akshaykalia-chd/Px-Rack/STL/PLA_PETG/25x265 Banding.stl

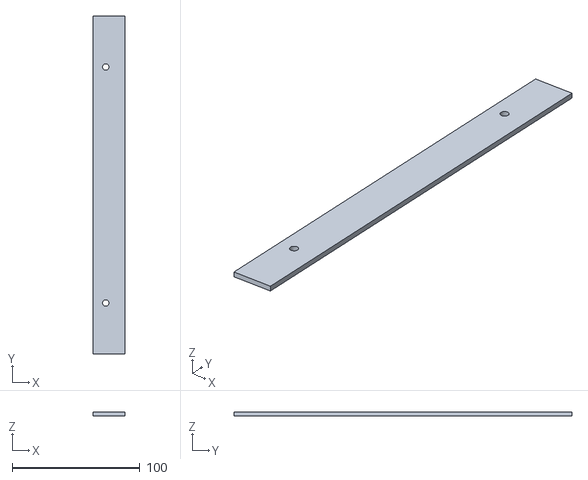
[picture p21: CAD file, 2026-06-15]
STL/PLA_PETG/25x265 Banding.stl
25.0 x 265.0 x 3.00
