akshaykalia-chd/Px-Rack/STL/ABS/Power-Mount-Back-Plate.stl

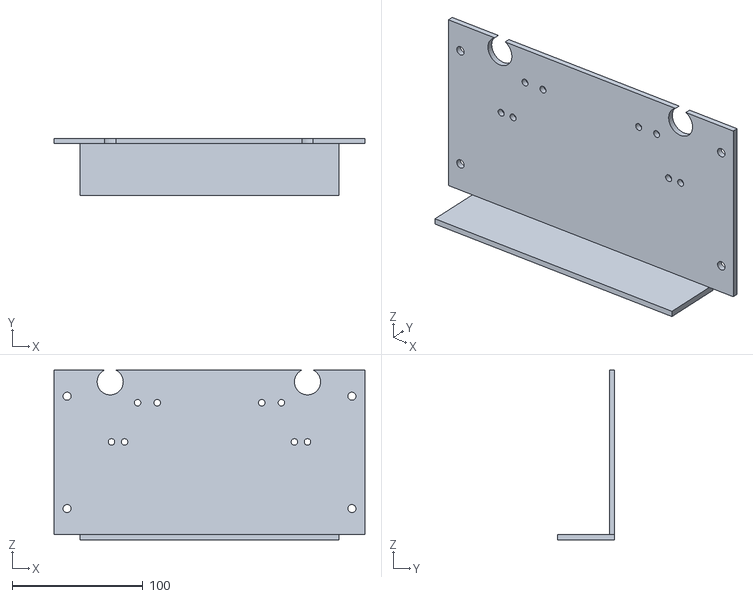
[picture p22: CAD file, 2026-06-15]
STL/ABS/Power-Mount-Back-Plate.stl
238.0 x 44.0 x 130.0
