akshaykalia-chd/Px-Rack/STL/PLA_PETG/5mm-Swith-bush.stl

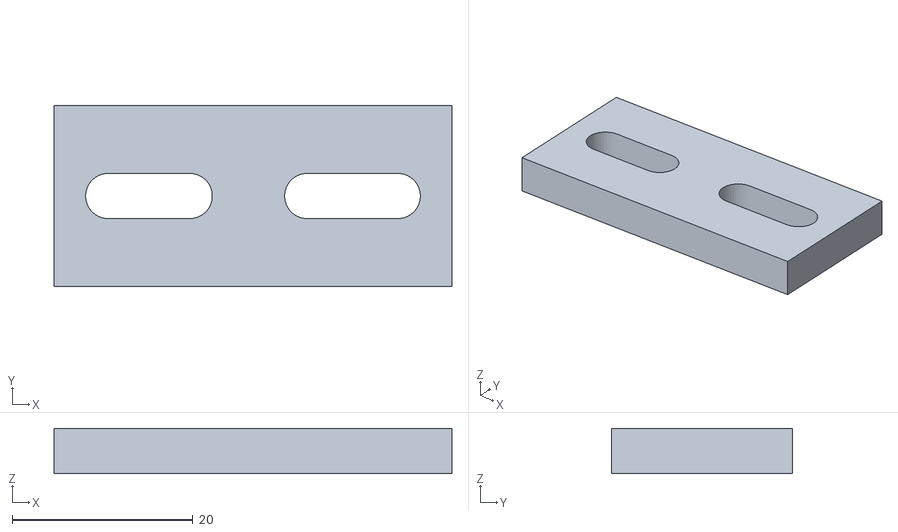
[picture p23: CAD file, 2026-06-15]
STL/PLA_PETG/5mm-Swith-bush.stl
44.0 x 20.0 x 5.00
