akshaykalia-chd/Px-Rack/STL/ABS/Foot.stl

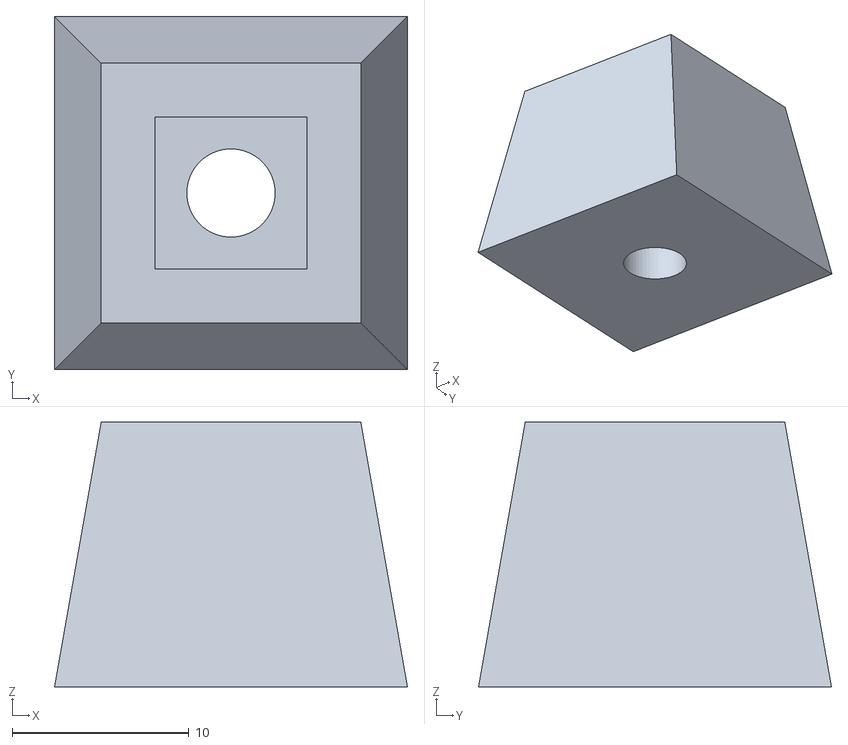
[picture p24: CAD file, 2026-05-14]
STL/ABS/Foot.stl
20.0 x 20.0 x 15.0
