akshaykalia-chd/Px-Rack/STL/PLA_PETG/Back-Cover.stl

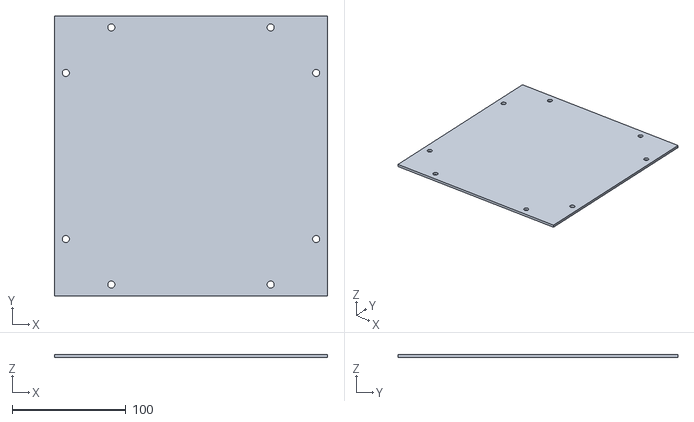
[picture p25: CAD file, 2026-06-15]
STL/PLA_PETG/Back-Cover.stl
240.0 x 246.0 x 3.00
