akshaykalia-chd/Px-Rack/STL/ABS/Power-Mount-PCB-Holder-Plate.stl

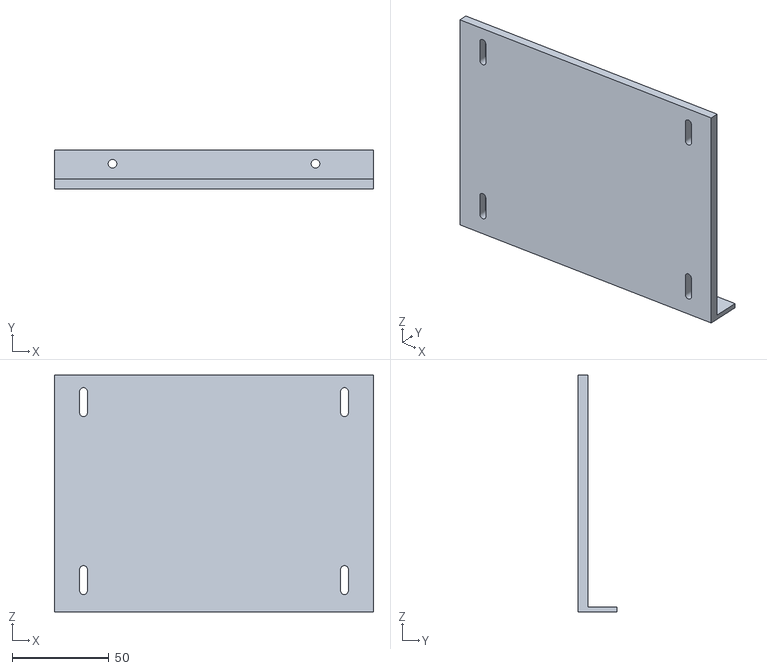
[picture p26: CAD file, 2026-04-22]
STL/ABS/Power-Mount-PCB-Holder-Plate.stl
165.0 x 20.0 x 122.5
