akshaykalia-chd/Px-Rack/STL/PLA_PETG/Bottom-cover.stl

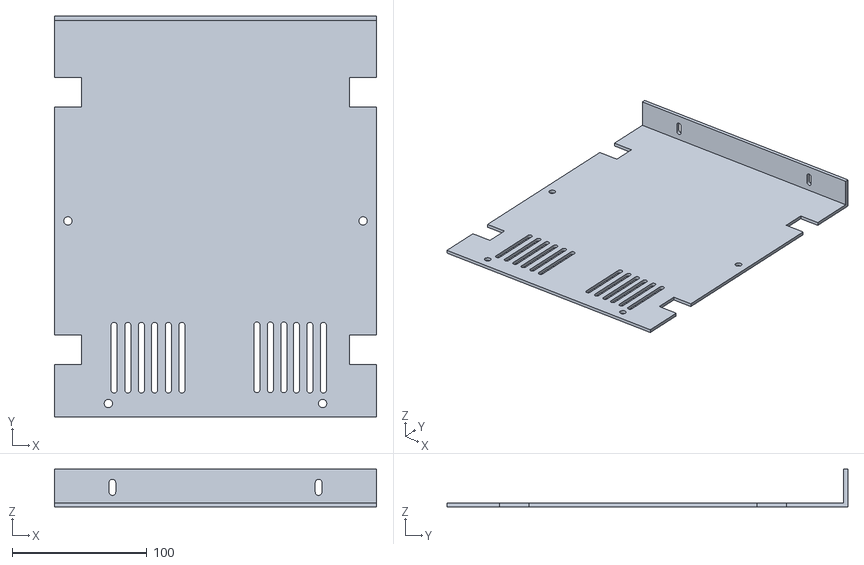
[picture p27: CAD file, 2026-06-15]
STL/PLA_PETG/Bottom-cover.stl
239.0 x 297.5 x 28.0
