akshaykalia-chd/Px-Rack/STL/ABS/Power-Mount-Base.stl

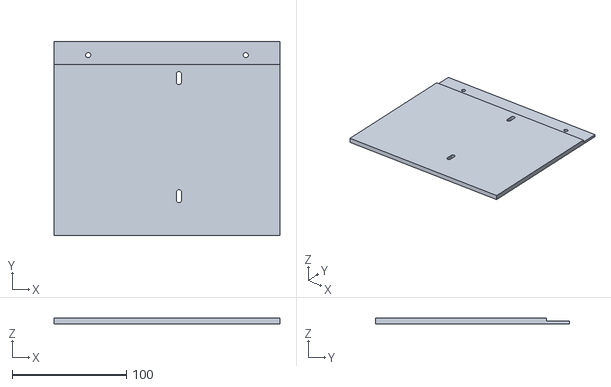
[picture p28: CAD file, 2026-04-22]
STL/ABS/Power-Mount-Base.stl
198.0 x 170.0 x 5.00
