akshaykalia-chd/Px-Rack/STL/PLA_PETG/Left-Side-Panel-120mm-Fan-Power-Cut.stl

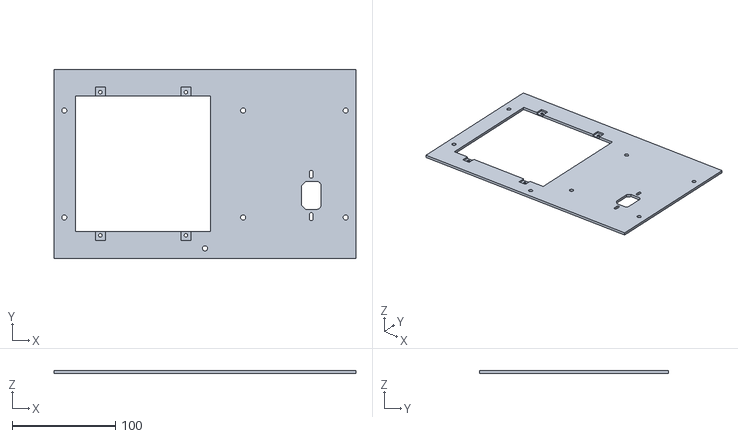
[picture p29: CAD file, 2026-06-15]
STL/PLA_PETG/Left-Side-Panel-120mm-Fan-Power-Cut.stl
293.0 x 183.8 x 3.00
