akshaykalia-chd/Px-Rack/STL/PLA_PETG/Top-Cover.stl

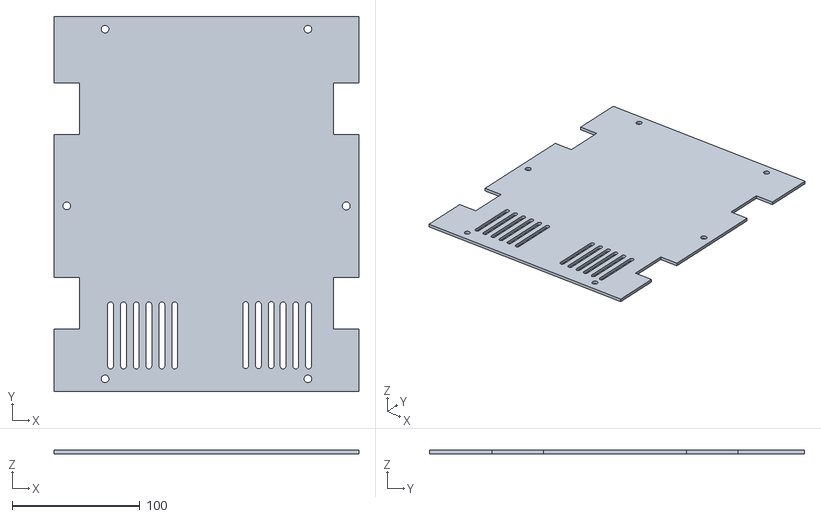
[picture p30: CAD file, 2026-06-15]
STL/PLA_PETG/Top-Cover.stl
239.0 x 294.0 x 3.00
