akshaykalia-chd/Px-Rack/STL/PLA_PETG/240mm-Banding.stl

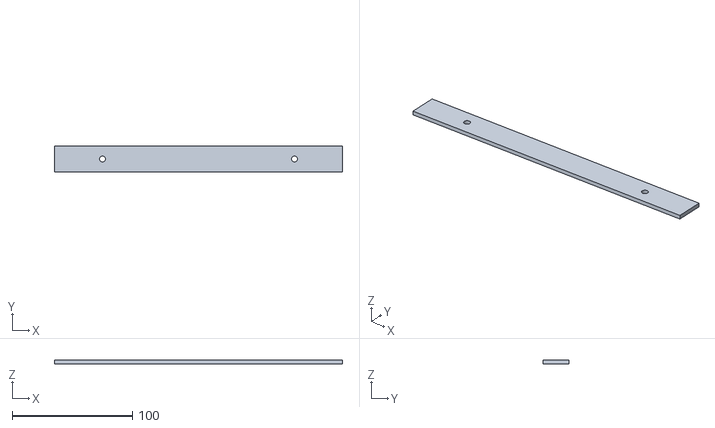
[picture p31: CAD file, 2026-06-15]
STL/PLA_PETG/240mm-Banding.stl
240.0 x 22.0 x 3.00
