akshaykalia-chd/Px-Rack/STL/PLA_PETG/Fan-Cut-120.stl

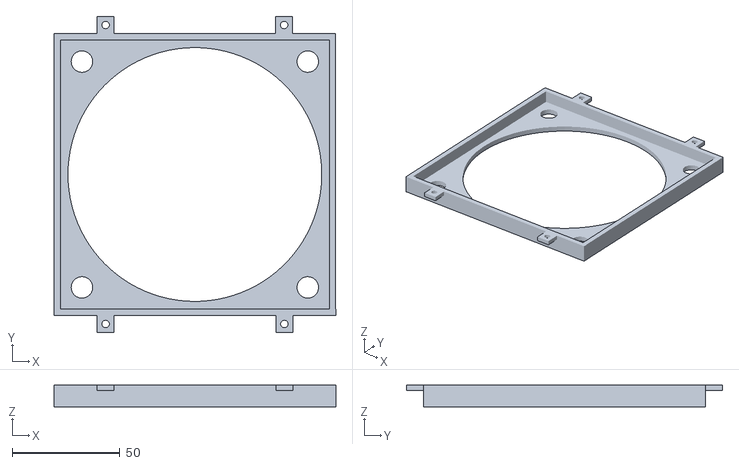
[picture p32: CAD file, 2026-05-14]
STL/PLA_PETG/Fan-Cut-120.stl
131.1 x 147.0 x 10.0
